Edlward/RC-Servo-Tester-/MCU_Source/Servo_Tester_v4/Source/drv_adc.c

#include "board.h"

/* Private define ------------------------------------------------------------*/
#define ADC1_DR_Address                0x40012440

/* Private macro -------------------------------------------------------------*/
/* Private variables ---------------------------------------------------------*/
//__IO uint32_t TempSensVoltmv = 0, VrefIntVoltmv = 0;
__IO uint16_t ADC_Value[2];

/* Private function prototypes -----------------------------------------------*/

/* Private functions ---------------------------------------------------------*/


void ADC_CH_DMA_Config(void)
{
  ADC_InitTypeDef     ADC_InitStructure;
  DMA_InitTypeDef     DMA_InitStructure;
  
  /* ADC1 DeInit */  
  ADC_DeInit(ADC1);
  
  /* ADC1 Periph clock enable */
  RCC_APB2PeriphClockCmd(RCC_APB2Periph_ADC1, ENABLE);
  
  /* DMA1 clock enable */
  RCC_AHBPeriphClockCmd(RCC_AHBPeriph_DMA1 , ENABLE);
  
  /* DMA1 Channel1 Config */
  DMA_DeInit(DMA1_Channel1);
  DMA_InitStructure.DMA_PeripheralBaseAddr = (uint32_t)ADC1_DR_Address;
  DMA_InitStructure.DMA_MemoryBaseAddr = (uint32_t)ADC_Value;
  DMA_InitStructure.DMA_DIR = DMA_DIR_PeripheralSRC;
  DMA_InitStructure.DMA_BufferSize = 2;
  DMA_InitStructure.DMA_PeripheralInc = DMA_PeripheralInc_Disable;
  DMA_InitStructure.DMA_MemoryInc = DMA_MemoryInc_Enable;
  DMA_InitStructure.DMA_PeripheralDataSize = DMA_PeripheralDataSize_HalfWord;
  DMA_InitStructure.DMA_MemoryDataSize = DMA_MemoryDataSize_HalfWord;
  DMA_InitStructure.DMA_Mode = DMA_Mode_Circular;
  DMA_InitStructure.DMA_Priority = DMA_Priority_High;
  DMA_InitStructure.DMA_M2M = DMA_M2M_Disable;
  DMA_Init(DMA1_Channel1, &DMA_InitStructure);
  
  /* DMA1 Channel1 enable */
  DMA_Cmd(DMA1_Channel1, ENABLE);
  
  /* ADC DMA request in circular mode */
  ADC_DMARequestModeConfig(ADC1, ADC_DMAMode_Circular);
  
  /* Enable ADC_DMA */
  ADC_DMACmd(ADC1, ENABLE);  
  
  /* Initialize ADC structure */
  ADC_StructInit(&ADC_InitStructure);
  
  /* Configure the ADC1 in continous mode withe a resolutuion equal to 12 bits  */
  ADC_InitStructure.ADC_Resolution = ADC_Resolution_12b;
  ADC_InitStructure.ADC_ContinuousConvMode = ENABLE; 
  ADC_InitStructure.ADC_ExternalTrigConvEdge = ADC_ExternalTrigConvEdge_None;
  ADC_InitStructure.ADC_DataAlign = ADC_DataAlign_Right;
  ADC_InitStructure.ADC_ScanDirection = ADC_ScanDirection_Backward;
  ADC_Init(ADC1, &ADC_InitStructure); 
 
  /* Convert the ADC1 temperature sensor  with 55.5 Cycles as sampling time */ 
  ADC_ChannelConfig(ADC1, ADC_Channel_1 , ADC_SampleTime_239_5Cycles);  
  ADC_TempSensorCmd(ENABLE);
  
  /* Convert the ADC1 Vref  with 55.5 Cycles as sampling time */ 
  ADC_ChannelConfig(ADC1, ADC_Channel_TempSensor , ADC_SampleTime_239_5Cycles); 
  ADC_VrefintCmd(ENABLE);
  
  /* ADC Calibration */
  ADC_GetCalibrationFactor(ADC1);
  
  /* Enable ADC1 */
  ADC_Cmd(ADC1, ENABLE);     
  
  /* Wait the ADRDY falg */
  while(!ADC_GetFlagStatus(ADC1, ADC_FLAG_ADRDY)); 
  
  /* ADC1 regular Software Start Conv */ 
  ADC_StartOfConversion(ADC1);
}


void adc_GPIO_Init(void) {
		GPIO_InitTypeDef GPIO_InitStructure;

		GPIO_InitStructure.GPIO_Pin = GPIO_Pin_1;			//ADC CH1
		GPIO_InitStructure.GPIO_Mode = GPIO_Mode_AN;
		GPIO_InitStructure.GPIO_Speed = GPIO_Speed_2MHz;
		//GPIO_InitStructure.GPIO_OType = GPIO_OType_PP;
		GPIO_InitStructure.GPIO_PuPd = GPIO_PuPd_NOPULL ;
		GPIO_Init(GPIOA, &GPIO_InitStructure);

	ADC_GetCalibrationFactor(ADC1);

//	
//    // ADC assumes all the GPIO was already placed in 'AIN' mode
//    DMA_DeInit(DMA1_Channel1);
//    DMA_InitStructure.DMA_PeripheralBaseAddr = (uint32_t)&ADC1->DR;
//    DMA_InitStructure.DMA_MemoryBaseAddr = (uint32_t)&ADC_value[0];					//adc dma address set
//    DMA_InitStructure.DMA_DIR = DMA_DIR_PeripheralSRC;
//    DMA_InitStructure.DMA_BufferSize = 2;//multiChannel ? 2 : 1;
//    DMA_InitStructure.DMA_PeripheralInc = DMA_PeripheralInc_Disable;
//    DMA_InitStructure.DMA_MemoryInc = DMA_MemoryInc_Enable ;//: DMA_MemoryInc_Disable;
//    DMA_InitStructure.DMA_PeripheralDataSize = DMA_PeripheralDataSize_HalfWord;
//    DMA_InitStructure.DMA_MemoryDataSize = DMA_MemoryDataSize_HalfWord;
//    DMA_InitStructure.DMA_Mode = DMA_Mode_Circular;
//    DMA_InitStructure.DMA_Priority = DMA_Priority_High;
//    DMA_InitStructure.DMA_M2M = DMA_M2M_Disable;
//    DMA_Init(DMA1_Channel1, &DMA_InitStructure);
//    /* Enable DMA1 channel1 */
//    DMA_Cmd(DMA1_Channel1, ENABLE);

//    ADC_InitStructure.ADC_Mode = ADC_Mode_Independent;
//    ADC_InitStructure.ADC_ScanConvMode = ENABLE;//multiChannel ? ENABLE : DISABLE;
//    ADC_InitStructure.ADC_ContinuousConvMode = ENABLE;
//    ADC_InitStructure.ADC_ExternalTrigConv = ADC_ExternalTrigConv_None;
//    ADC_InitStructure.ADC_DataAlign = ADC_DataAlign_Right;
//    ADC_InitStructure.ADC_NbrOfChannel = 2;//multiChannel ? 2 : 1;
//    ADC_Init(ADC1, &ADC_InitStructure);

//    ADC_RegularChannelConfig(ADC1, ADC_CH1_Channel, 1, ADC_SampleTime_28Cycles5);		//ADC CH1
//    ADC_RegularChannelConfig(ADC1, ADC_CH2_Channel, 2, ADC_SampleTime_28Cycles5);		//ADC CH2
//	
//// 	for(i=0; i<2;i++) {
//// 			ADC_RegularChannelConfig(ADC1, i, 2, ADC_SampleTime_239Cycles5);

//// 	}

////   ADC_RegularChannelConfig(ADC1,ADC_Channel_11, 1, ADC_SampleTime_28Cycles5);




//		ADC_DMACmd(ADC1, ENABLE);

//    ADC_Cmd(ADC1, ENABLE);

//    // Calibrate ADC
//    ADC_ResetCalibration(ADC1);
//    while(ADC_GetResetCalibrationStatus(ADC1));
//    ADC_StartCalibration(ADC1);
//    while(ADC_GetCalibrationStatus(ADC1));

//    // Fire off ADC
//    ADC_SoftwareStartConvCmd(ADC1, ENABLE);
}
