Edlward/RC-Servo-Tester-/MCU_Source/Servo_Tester_v4/Source/drv_keyInput.c

#include "board.h"

//PUSH SWITCH INPUT : PA5 

 void EXTI_Config(void)
{
  EXTI_InitTypeDef   EXTI_InitStructure;
  GPIO_InitTypeDef   GPIO_InitStructure;
  NVIC_InitTypeDef   NVIC_InitStructure;
  
  /* Enable GPIOA clock */
  RCC_AHBPeriphClockCmd(RCC_AHBPeriph_GPIOA, ENABLE);

  /* Configure PA0 pin as input floating */
  GPIO_InitStructure.GPIO_Pin = GPIO_Pin_5;
  GPIO_InitStructure.GPIO_Speed = GPIO_Speed_2MHz;
  GPIO_InitStructure.GPIO_Mode = GPIO_Mode_IN;
  GPIO_InitStructure.GPIO_PuPd = GPIO_PuPd_UP;
  GPIO_Init(GPIOA, &GPIO_InitStructure);

  /* Enable SYSCFG clock */
  RCC_APB2PeriphClockCmd(RCC_APB2Periph_SYSCFG, ENABLE);
  
  /* Connect EXTI0 Line to PA0 pin */
  SYSCFG_EXTILineConfig(EXTI_PortSourceGPIOA, EXTI_PinSource5);

  /* Configure EXTI0 line */
  EXTI_InitStructure.EXTI_Line = EXTI_Line5;
  EXTI_InitStructure.EXTI_Mode = EXTI_Mode_Interrupt;
  EXTI_InitStructure.EXTI_Trigger = EXTI_Trigger_Falling;
  EXTI_InitStructure.EXTI_LineCmd = ENABLE;
  EXTI_Init(&EXTI_InitStructure);

  /* Enable and set EXTI0 Interrupt */
  NVIC_InitStructure.NVIC_IRQChannel = EXTI4_15_IRQn;
  NVIC_InitStructure.NVIC_IRQChannelPriority = 0x00;
  NVIC_InitStructure.NVIC_IRQChannelCmd = ENABLE;
  NVIC_Init(&NVIC_InitStructure);
}




void EXTI4_15_IRQHandler(void)
{
  if(EXTI_GetITStatus(EXTI_Line5) != RESET)
  {
    /* Toggle LED3 and LED4 */
    EXTI_ClearITPendingBit(EXTI_Line5);
	//	delay(50);
		mode_Change();
    /* Clear the EXTI line 0 pending bit */
  }
}
